saawsm/SW22/docs/images/output/SW2O1.png

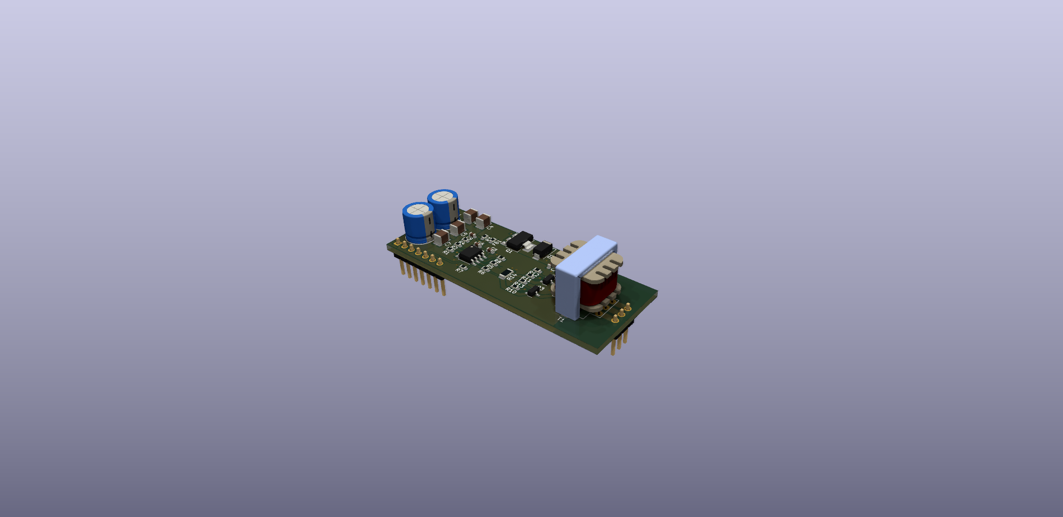
docs/images/output/SW2O1.png
