saawsm/SW22/docs/images/SW2F1_populated_back.png

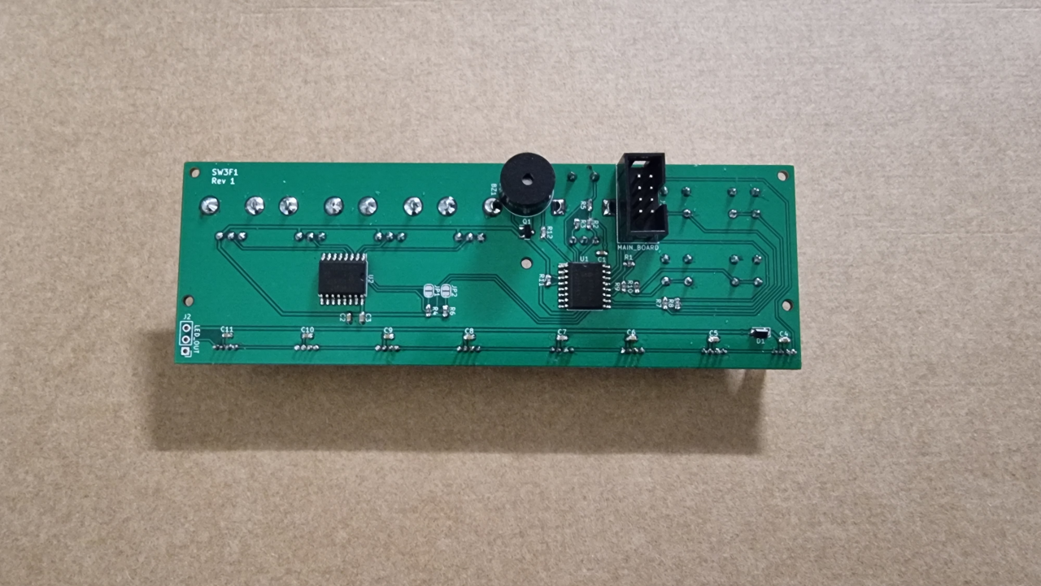
docs/images/SW2F1_populated_back.png
