saawsm/SW22/docs/images/SW2F1_populated_front.png

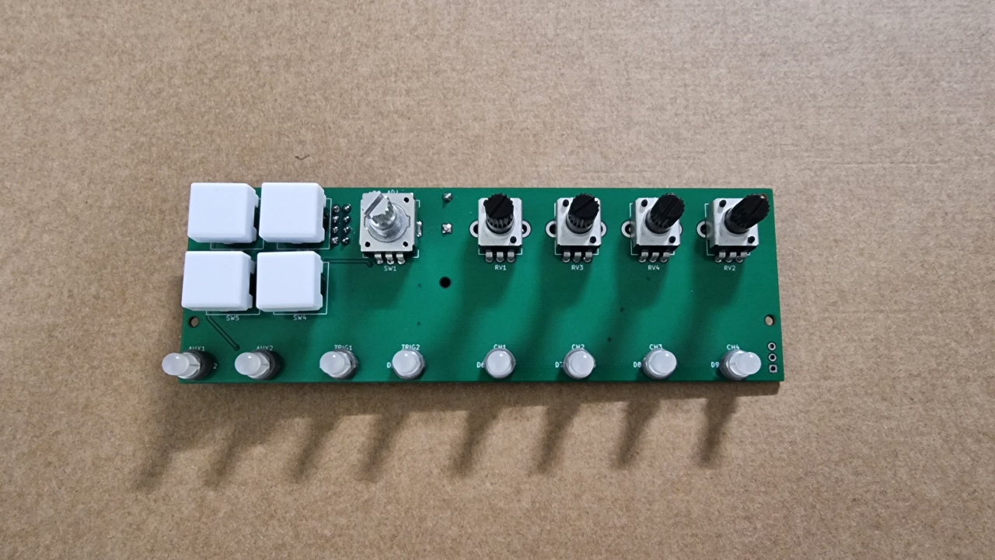
docs/images/SW2F1_populated_front.png
