saawsm/SW22/docs/images/SW2F1_populated_led_spacers.png

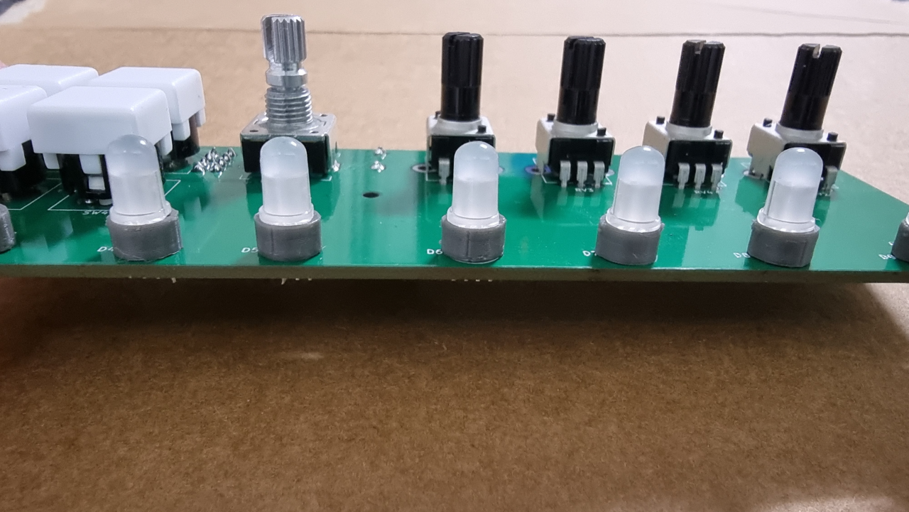
docs/images/SW2F1_populated_led_spacers.png
