saawsm/SW22/docs/images/SW2O2.png

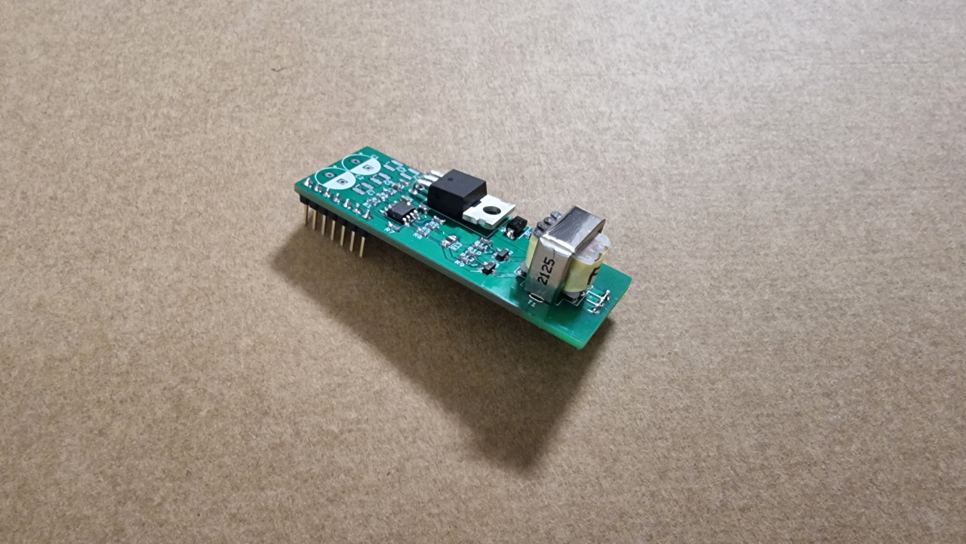
docs/images/SW2O2.png
