saawsm/SW22/docs/images/SW2X1.png

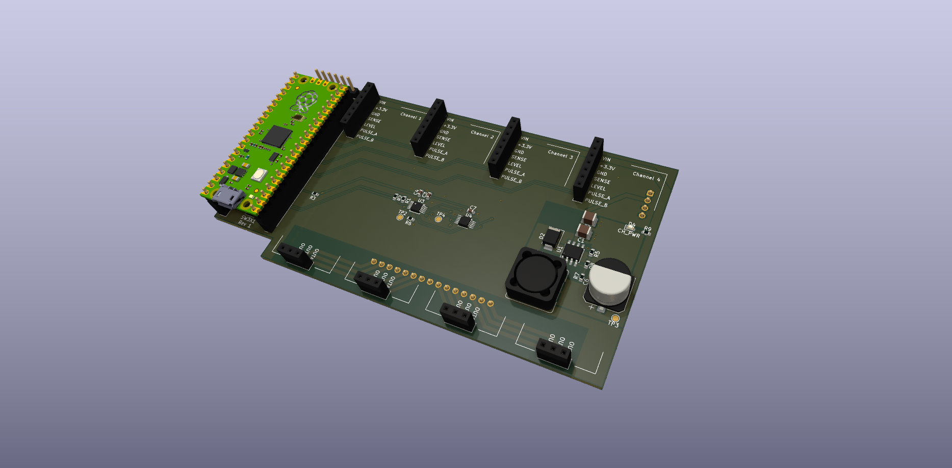
docs/images/SW2X1.png
