saawsm/SW22/docs/images/SW2X1_smd_populated.png

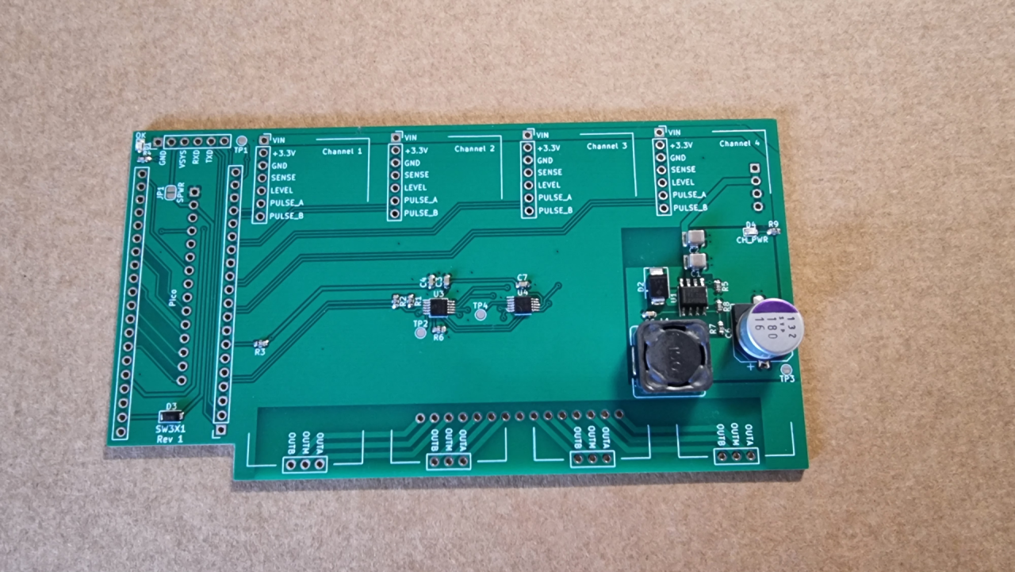
docs/images/SW2X1_smd_populated.png
