saawsm/SW22/docs/images/SW22_smd_populated.png

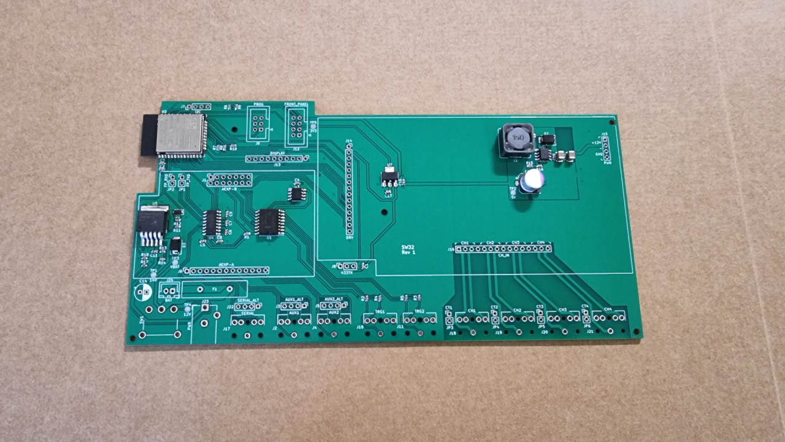
docs/images/SW22_smd_populated.png
