saawsm/SW22/docs/images/SW22_stacked.png

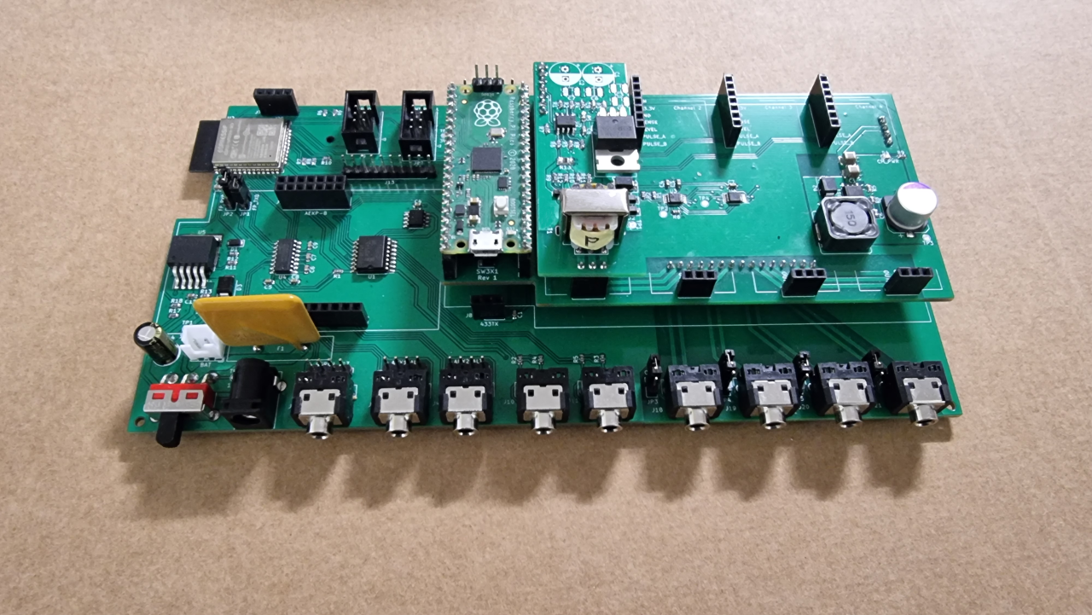
docs/images/SW22_stacked.png
