saawsm/SW22/docs/images/SW22_unpopulated.png

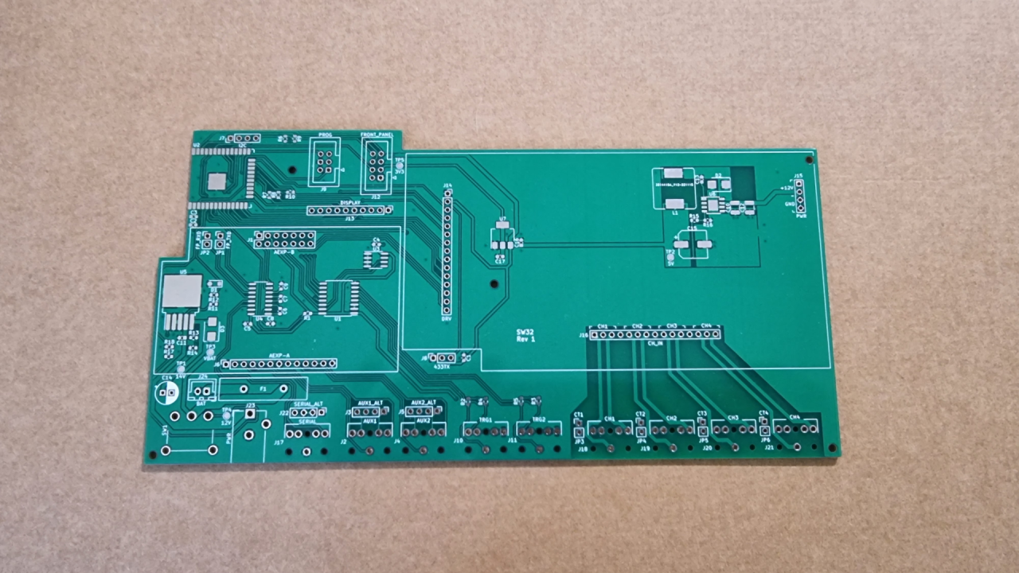
docs/images/SW22_unpopulated.png
