saawsm/SW22/docs/images/SW22_debug_oled.png

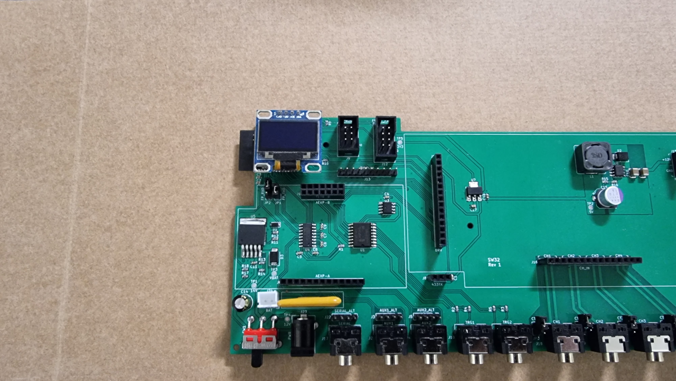
docs/images/SW22_debug_oled.png
