saawsm/SW22/hardware/pcb/modules/audio/SW-32MA1/SW-32MA1.kicad_sch

## KiCad design hardware/pcb/modules/audio/SW-32MA1/SW-32MA1.kicad_sch (2022-04-07)

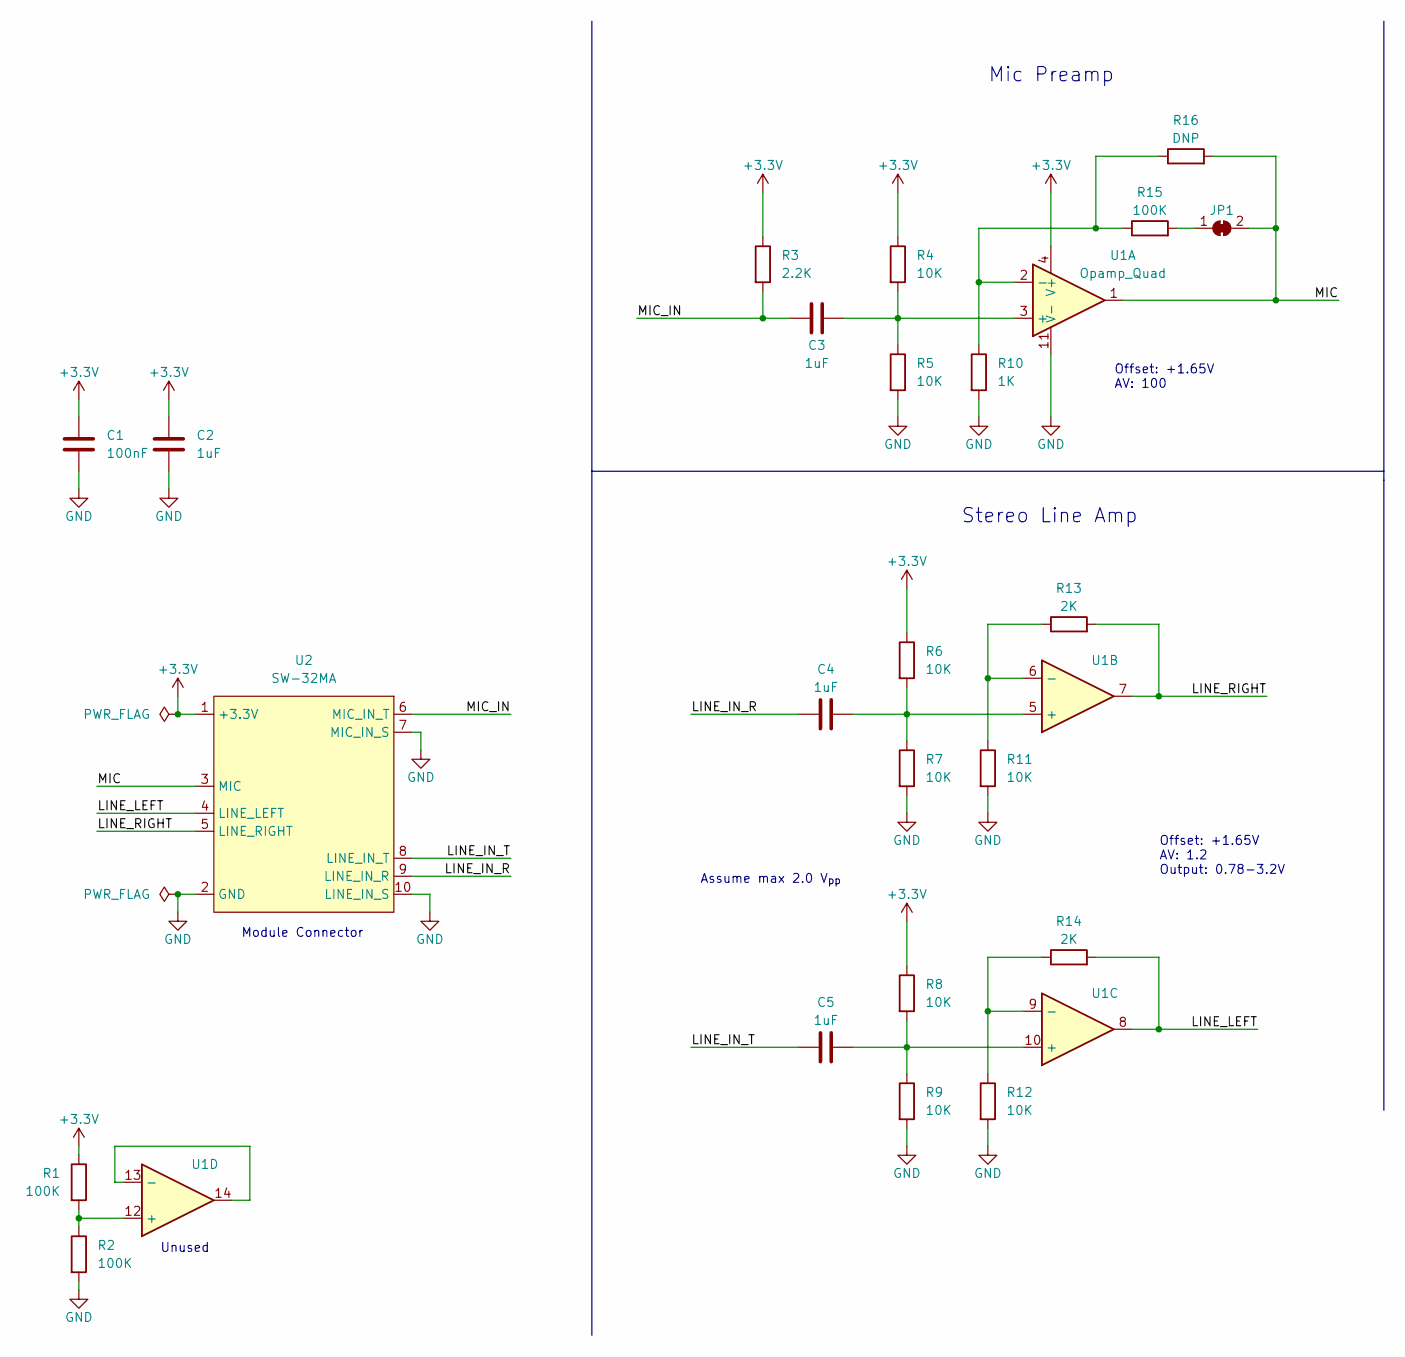
[picture p43: schematic SW-32MA1.kicad_sch]

Parts:
C1: 100nF; C_0603_1608Metric
C2, C3, C4, C5: 1uF; C_0603_1608Metric
JP1: SolderJumper_2_Bridged; SolderJumper-2_P1.3mm_Bridged_RoundedPad1.0x1.5mm
R1, R2, R15: 100K; R_0603_1608Metric
R3: 2.2K; R_0603_1608Metric
R4, R5, R6, R7, R8, R9, R11, R12: 10K; R_0603_1608Metric
R10: 1K; R_0603_1608Metric
R13, R14: 2K; R_0603_1608Metric
R16: DNP; R_Axial_DIN0204_L3.6mm_D1.6mm_P5.08mm_Horizontal
U1: Opamp_Quad; SOIC-14_3.9x8.7mm_P1.27mm
U2: SW-32MA; SW-32MA_Header

Connections:
+3.3V: C1.2, C2.2, R1.1, R3.1, R4.1, R6.1, R8.1, U1.4 (V+), U2.1 (+3.3V)
GND: C1.1, C2.1, R2.2, R5.2, R7.2, R9.2, R10.2, R11.2, R12.2, U1.11 (V-), U2.2 (GND), U2.7 (MIC_IN_S), U2.10 (LINE_IN_S)
LINE_IN_R: C4.1, U2.9 (LINE_IN_R)
LINE_IN_T: C5.1, U2.8 (LINE_IN_T)
LINE_LEFT: R14.2, U1.8, U2.4 (LINE_LEFT)
LINE_RIGHT: R13.2, U1.7, U2.5 (LINE_RIGHT)
MIC: JP1.2 (B), R16.2, U1.1, U2.3 (MIC)
MIC_IN: C3.1, R3.2, U2.6 (MIC_IN_T)
unnamed: C3.2, R4.2, R5.1, U1.3 (+)
unnamed: C4.2, R6.2, R7.1, U1.5 (+)
unnamed: C5.2, R8.2, R9.1, U1.10 (+)
unnamed: JP1.1 (A), R15.2
unnamed: R1.2, R2.1, U1.12 (+)
unnamed: R10.1, R15.1, R16.1, U1.2 (-)
unnamed: R11.1, R13.1, U1.6 (-)
unnamed: R12.1, R14.1, U1.9 (-)
unnamed: U1.13 (-), U1.14

Notes on the sheet:
Stereo Line Amp
Assume max 2.0 V_{pp}
Mic Preamp
Module Connector
Offset: +1.65V AV: 1.2 Output: 0.78-3.2V
Offset: +1.65V AV: 100
Unused
